Esdras2/dspic30f-devboard-kit/docs/002_puerto_icsp.png

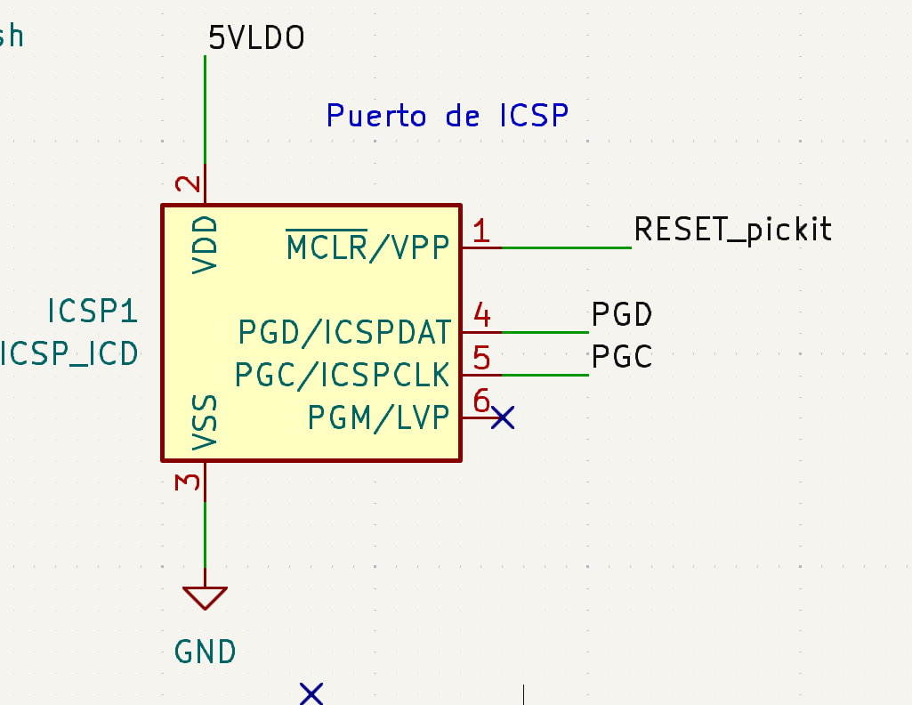
docs/002_puerto_icsp.png
