Esdras2/dspic30f-devboard-kit/docs/004_cap_desacople.png

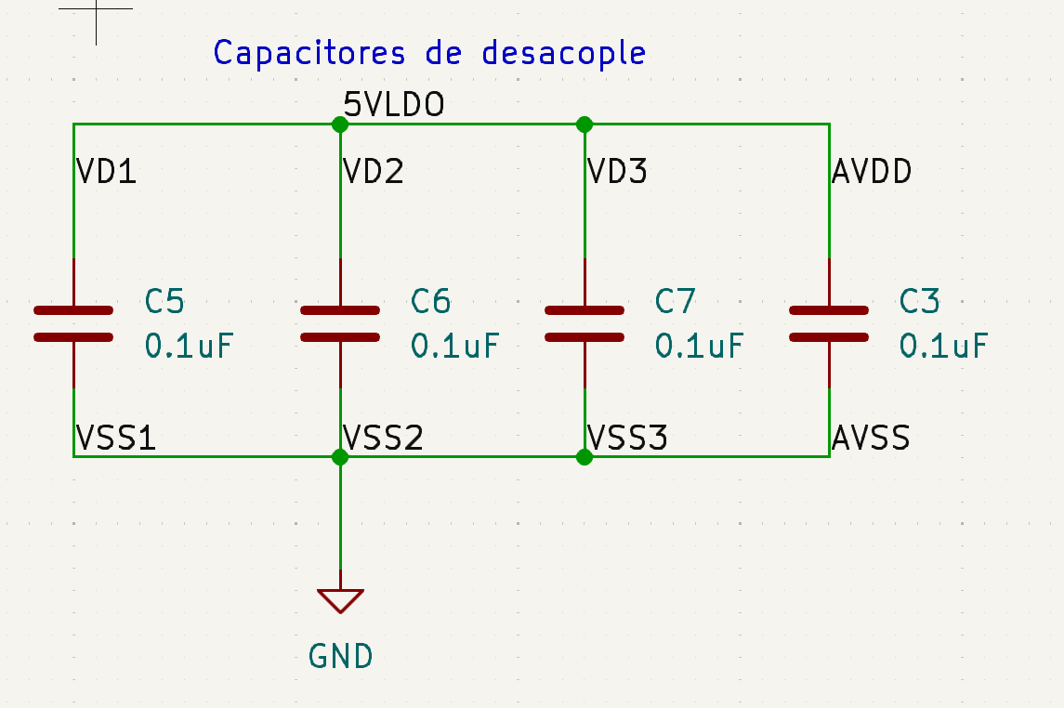
docs/004_cap_desacople.png
