Esdras2/dspic30f-devboard-kit/docs/PCB_board_rev_a.png

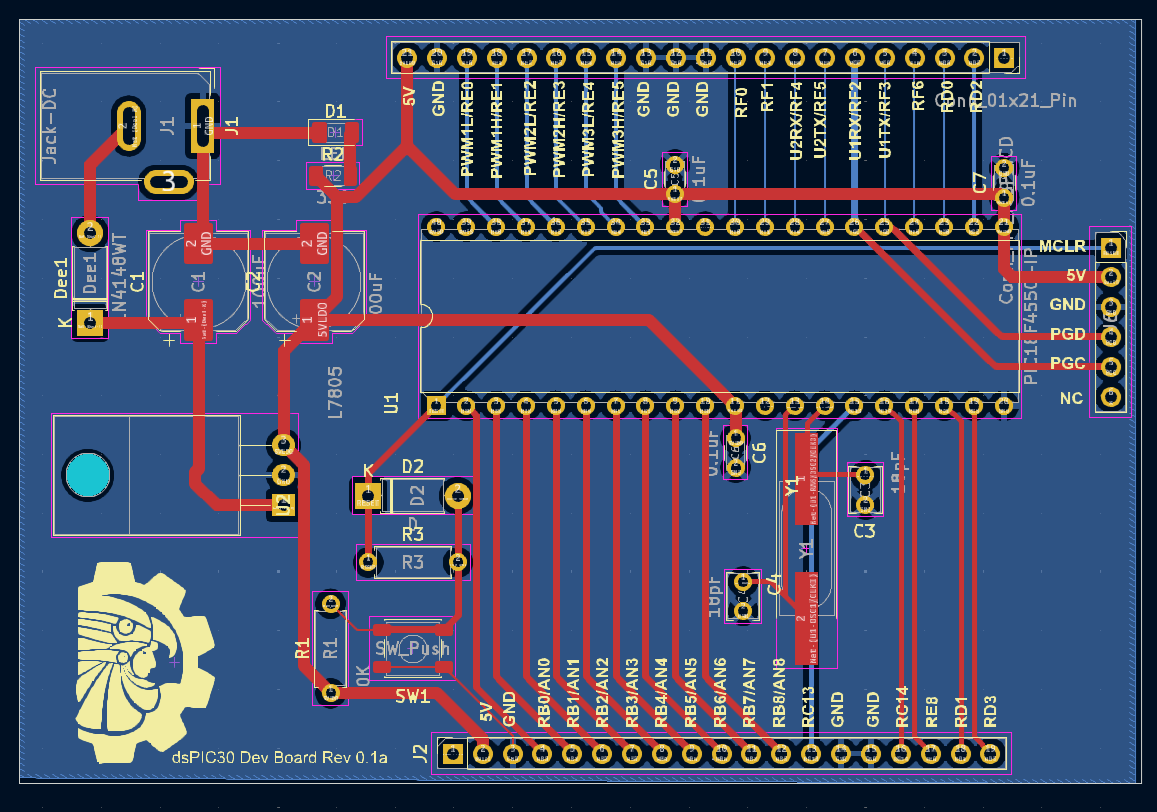
docs/PCB_board_rev_a.png
