Esdras2/dspic30f-devboard-kit/docs/PCB_board_rev_d.png

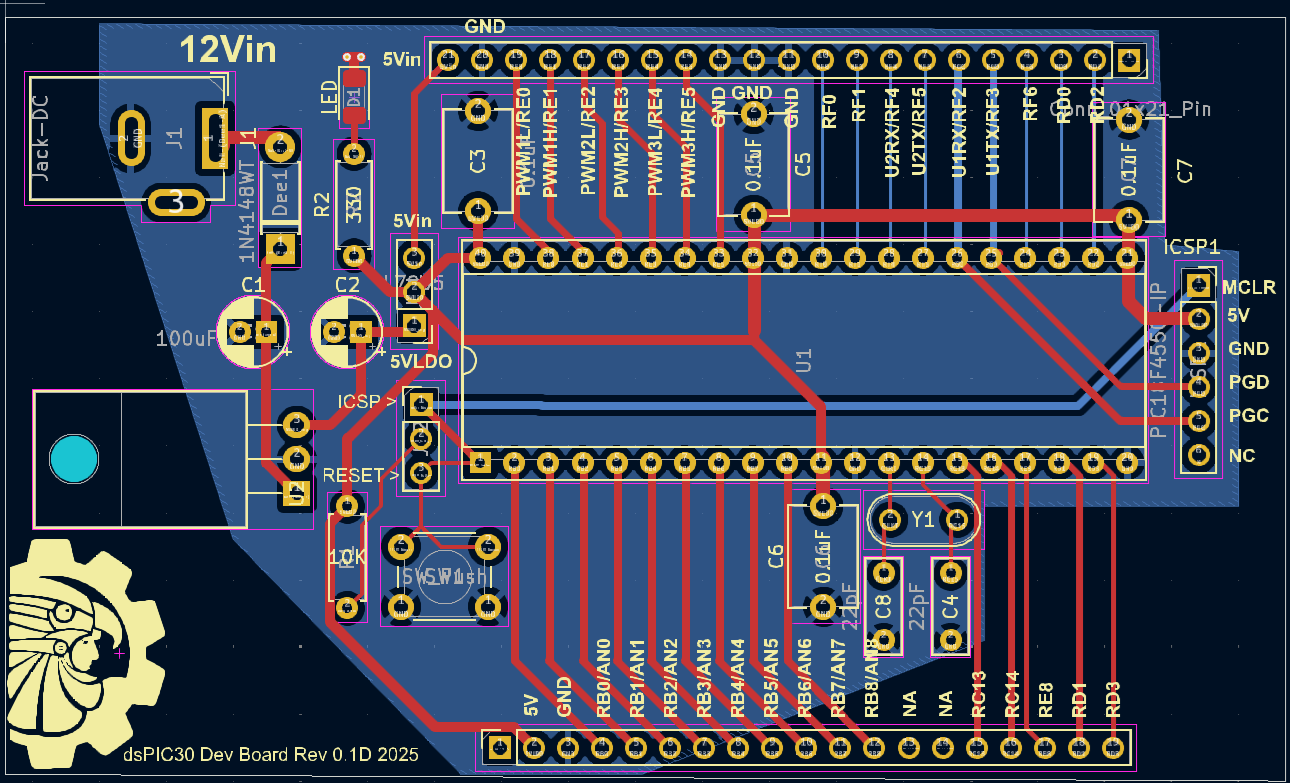
docs/PCB_board_rev_d.png
