Esdras2/dspic30f-devboard-kit/docs/visor_3d_rev_b.png

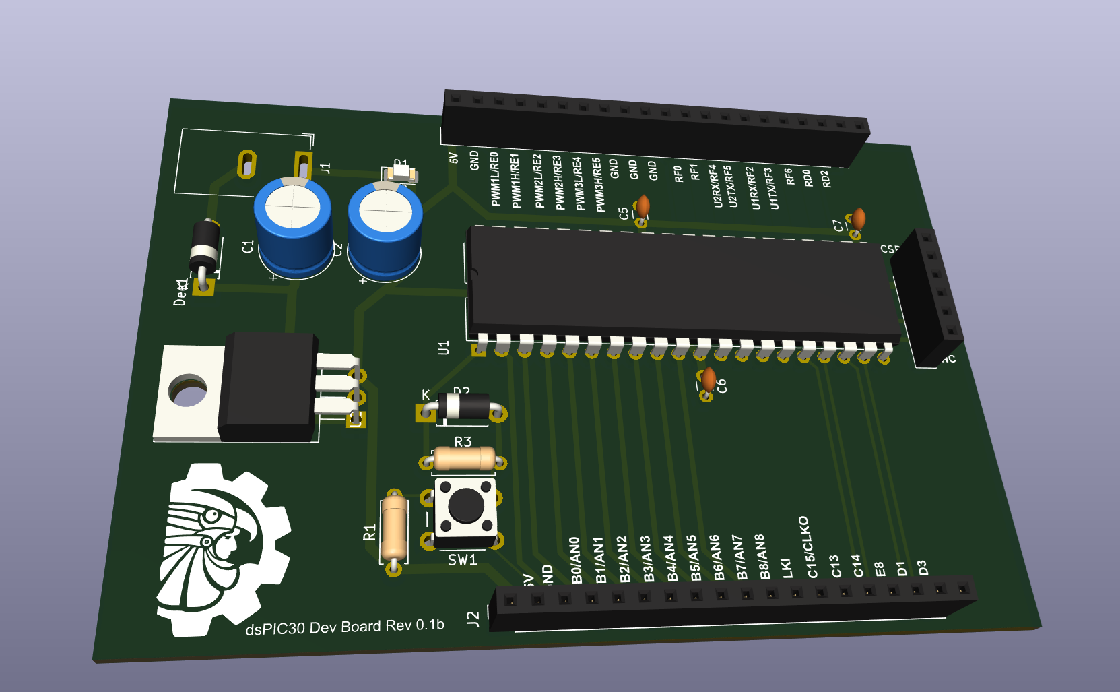
docs/visor_3d_rev_b.png
